wiekstras/FpvDeck/hardware/research/SBC_COMPARISON.md

# Compute platform comparison

## Prototype 0 decision

**Raspberry Pi 5 2 GB is selected for the functionality bench.** It is not a
production SoM decision. Compared with Pi Zero 2 W, it has enough CPU margin for
USB analog capture, Qt composition and software experimentation; compared with
Pi 4 2 GB, the current EU price premium is small. Its MIPI connector supports the
selected official Touch Display 2 while USB-A accepts the documented capture
device. A Compute Module adds carrier work without helping tonight's objective.

| Prototype 0 candidate | Practical result | Decision |
|---|---|---|
| Raspberry Pi 5 2 GB | 2.4 GHz Cortex-A76, USB 3/2, dual MIPI, current Pi OS; €68.90 in-stock snapshot | **SELECTED**: best iteration/performance balance |
| Raspberry Pi 4 2 GB | lower power and adequate basic capture; €57.90-class listing | Rejected: modest saving for much less CPU margin |
| Raspberry Pi Zero 2 W | tiny/low power but 512 MB, micro-USB host adapters and limited compositor headroom | Rejected: avoidable bring-up constraints |
| Compute Module 4 + IO board | relevant to Prototype 1 CSI work | Rejected for Prototype 0: slower and more expensive to assemble |

| Candidate | Video/display and codec | Linux/support | Power/complexity | Availability/cost | Decision |
| --- | --- | --- | --- | --- | --- |
| Raspberry Pi CM4, BCM2711 | 2/4-lane CSI and DSI; H.264 1080p30 encode; OpenGL ES 3 | Raspberry Pi documents ADV728x-M; exceptional community | moderate, simple prototype carrier ecosystem | production stated through Jan 2034; roughly €35–90 by RAM/eMMC | **Prototype 1 selected** |
| Raspberry Pi CM5, BCM2712 | two flexible 4-lane CSI/DSI; stronger CPU/GPU; no CM4-style documented H.264 encode assumption | current Pi stack; ADV728x path needs CM5-specific validation | higher peak/thermal; carrier compatible conceptually, not electrically identical | current/available; roughly €55–130 | reject as baseline; benchmark |
| NXP i.MX 8M Plus SoM | dual 4-lane CSI, DSI/LVDS/HDMI; 1080p60 H.264/H.265 encode; 2D/3D GPU | NXP BSP/mainline mix; decoder porting work | industrial carrier/BSP effort; good codec fit | active; SoMs often €90–180 | **production lead** |
| NXP i.MX 8M Mini SoM | CSI/DSI and 1080p60 H.264 encode | mature embedded vendors | lower compute than Plus, still custom BSP | active; midrange | credible fallback |
| Rockchip RK3566/3568 SoM | CSI/DSI/LVDS variants, capable VPU/GPU | vendor kernels vary; exact interlaced/bridge support risky | attractive power/cost but integration variance | many modules, lifecycle varies | reject for Prototype 1 |
| TI AM62x SoM | CSI/DSI variants, industrial focus; multimedia differs by SKU | strong industrial docs/Yocto | good lifecycle, weaker DVR fit without exact codec SKU | industrial cost | retain for low-power study |

Selection is coupled to decoder and panel driver evidence. A CSI connector alone
does not prove the receiver accepts the decoder's data type/timing, and a VPU block
does not prove a maintained V4L2 encoder path.

Sources: [CM4 brief](https://datasheets.raspberrypi.com/cm4/cm4-product-brief.pdf),
[CM5 datasheet](https://pip.raspberrypi.com/categories/944-raspberry-pi-compute-module-5),
[i.MX 8M Plus](https://www.nxp.com/products/i.MX8MPLUS).
